maxfierke/gbtty/gb/src/portfolio.c

/*
 * Portfolio 6x8 converted to 8x8 1bpp tiles using PixelFont Editor
 *
 * Based on FON remake by VileR, licensed under CC-BY-SA 4.0.
 * Original source:
 * https://int10h.org/oldschool-pc-fonts/fontlist/font?portfolio_6x8
 */

#include <gbdk/platform.h>
#include <stdint.h>

BANKREF(portfolio)

const uint8_t portfolio_tiles[2048] = {
    0x00, 0x00, 0x00, 0x00, 0x00, 0x00, 0x00, 0x00,  // Char 000 (.)
    0x70, 0x88, 0xd8, 0x88, 0xf8, 0x88, 0x70, 0x00,  // Char 001 (.)
    0x70, 0xf8, 0xa8, 0xf8, 0x88, 0xf8, 0x70, 0x00,  // Char 002 (.)
    0x00, 0xd8, 0xf8, 0xf8, 0xf8, 0x70, 0x20, 0x00,  // Char 003 (.)
    0x00, 0x20, 0x70, 0xf8, 0x70, 0x20, 0x00, 0x00,  // Char 004 (.)
    0x70, 0x70, 0xf8, 0xd8, 0xd8, 0x20, 0x70, 0x00,  // Char 005 (.)
    0x20, 0x70, 0xf8, 0xf8, 0xf8, 0x20, 0x70, 0x00,  // Char 006 (.)
    0x00, 0x00, 0x00, 0x30, 0x30, 0x00, 0x00, 0x00,  // Char 007 (.)
    0xfc, 0xfc, 0xfc, 0xcc, 0xcc, 0xfc, 0xfc, 0xfc,  // Char 008 (.)
    0x00, 0x00, 0x30, 0x48, 0x48, 0x30, 0x00, 0x00,  // Char 009 (.)
    0xfc, 0xfc, 0xcc, 0xb4, 0xb4, 0xcc, 0xfc, 0xfc,  // Char 010 (.)
    0x38, 0x18, 0x28, 0x70, 0x88, 0x88, 0x70, 0x00,  // Char 011 (.)
    0x70, 0x88, 0x88, 0x70, 0x20, 0x70, 0x20, 0x00,  // Char 012 (.)
    0x38, 0x28, 0x38, 0x20, 0x20, 0xe0, 0xc0, 0x00,  // Char 013 (.)
    0x78, 0x48, 0x78, 0x48, 0x58, 0xd8, 0xc0, 0x00,  // Char 014 (.)
    0x20, 0xa8, 0x70, 0xd8, 0x70, 0xa8, 0x20, 0x00,  // Char 015 (.)
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
    0xd8, 0xd9, 0xda, 0xdb, 0xdc, 0xdd, 0xde, 0xdf, 0xe0, 0xe1, 0xe2, 0xe3,
    0xe4, 0xe5, 0xe6, 0xe7, 0xe8, 0xe9, 0xea, 0xeb, 0xec, 0xed, 0xee, 0xef,
    0xf0, 0xf1, 0xf2, 0xf3, 0xf4, 0xf5, 0xf6, 0xf7, 0xf8, 0xf9, 0xfa, 0xfb,
    0xfc, 0xfd, 0xfe, 0xff,
};
